denjhang/MegaGRRL-Desktop-Mini-USB/Silk Screen Art/sshot-20240607-222436.png

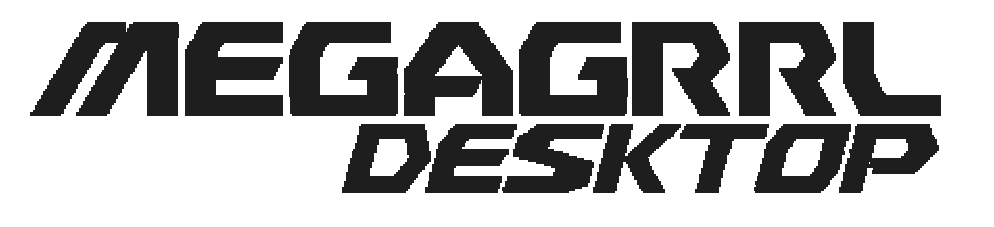
Silk Screen Art/sshot-20240607-222436.png
