denjhang/MegaGRRL-Desktop-Mini-USB/Silk Screen Art/sshot-20240607-222447.png

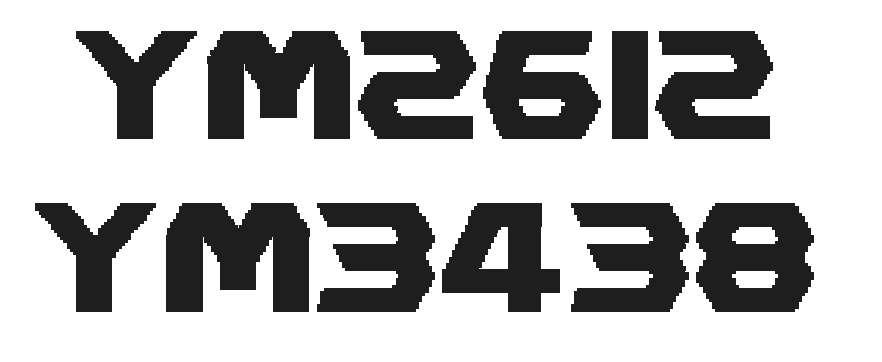
Silk Screen Art/sshot-20240607-222447.png
