denjhang/MegaGRRL-Desktop-Mini-USB/Silk Screen Art/电江开源数码.png

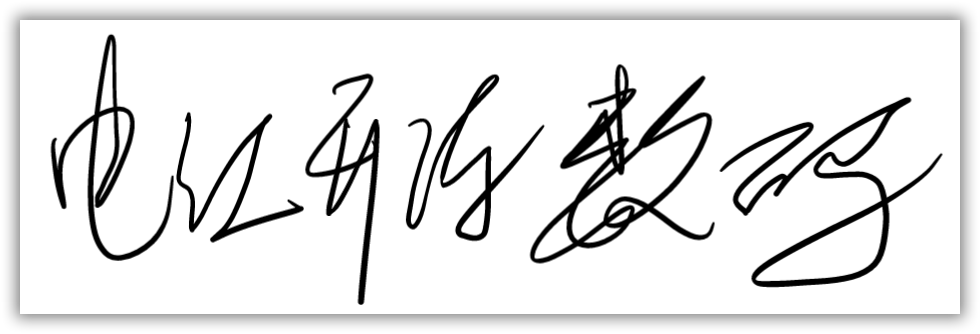
Silk Screen Art/电江开源数码.png
